Jan-Aarela/Salama-64/src/kuviot.h

#ifndef KUVIOT_H
#define KUVIOT_H

#include <stdint.h>

void kaikki(uint16_t tila);

void kirkkaustesti();

void himmennys(uint16_t kerrat, uint8_t nopeus);

void ympari(uint8_t kerrat, uint8_t nopeus);

void onebyone(uint16_t kerrat, uint8_t nopeus);

void taytto(uint16_t kerrat, uint8_t nopeus);

void tyhjennys(uint8_t nopeus);

void viivat(uint16_t kerrat, uint8_t nopeus);

void viivatk(uint16_t kerrat, uint8_t nopeus);

void kolari(uint16_t kerrat, uint8_t nopeus);

void kaks(uint16_t kerrat, uint8_t nopeus);

void kolmiot(uint16_t kerrat, uint8_t nopeus);

void kolmiotk(uint16_t kerrat, uint8_t nopeus);

void alas(uint16_t kerrat, uint8_t nopeus);

void vastakkain(uint16_t kerrat, uint8_t nopeus);

void strobe(uint16_t kerrat, uint8_t nopeus);

void kukka(uint16_t kerrat, uint8_t nopeus);

void kukka2(uint16_t kerrat, uint8_t nopeus);

#endif
