Jan-Aarela/Salama-64/src/lediportit.h

// vim: foldmethod=marker ft=c

// Tuodaan muut tiedostot.
#include <avr/io.h>
#include <stdint.h>

// Pinnit off tilassa 76543210
uint8_t alloff_pb = 0b11111111;

// Esim. 46. led toimii kun PA5 HIGH ja PB4 LOW.

// A PORTIT {{{
uint8_t pa[64] = {
    0b00000001, // 0.
    0b00000001,
    0b00000001,
    0b00000001,
    0b00000001,
    0b00000001,
    0b00000001,
    0b00000001,
    0b00000010,
    0b00000010, // 10.
    0b00000010,
    0b00000010,
    0b00000010,
    0b00000010,
    0b00000010,
    0b00000010,
    0b00000100,
    0b00000100,
    0b00000100,
    0b00000100, // 20.
    0b00000100,
    0b00000100,
    0b00000100,
    0b00000100,
    0b00001000,
    0b00001000,
    0b00001000,
    0b00001000,
    0b00001000,
    0b00001000, // 30.
    0b00001000,
    0b00001000,
    0b00010000,
    0b00010000,
    0b00010000,
    0b00010000,
    0b00010000,
    0b00010000,
    0b00010000,
    0b00010000, // 40.
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
};
// }}}

// B PORTIT {{{
uint8_t pb[64] = {
    0b11111110, // 1. led
    0b11111101,
    0b11111011,
    0b11110111,
    0b11101111,
    0b11011111,
    0b10111111,
    0b01111111,
    0b11111110,
    0b11111101, // 10.
    0b11111011,
    0b11110111,
    0b11101111,
    0b11011111,
    0b10111111,
    0b01111111,
    0b11111110,
    0b11111101,
    0b11111011,
    0b11110111, // 20.
    0b11101111,
    0b11011111,
    0b10111111,
    0b01111111,
    0b11111110,
    0b11111101,
    0b11111011,
    0b11110111,
    0b11101111,
    0b11011111, // 30.
    0b10111111,
    0b01111111,
    0b11111110,
    0b11111101,
    0b11111011,
    0b11110111,
    0b11101111,
    0b11011111,
    0b10111111,
    0b01111111, // 40.
    0b11111110,
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
};
// }}}

// Vittu mikä työmaa
